viamrobotics/Rover-VR1/CAD/VR1-22-0026.SLDPRT

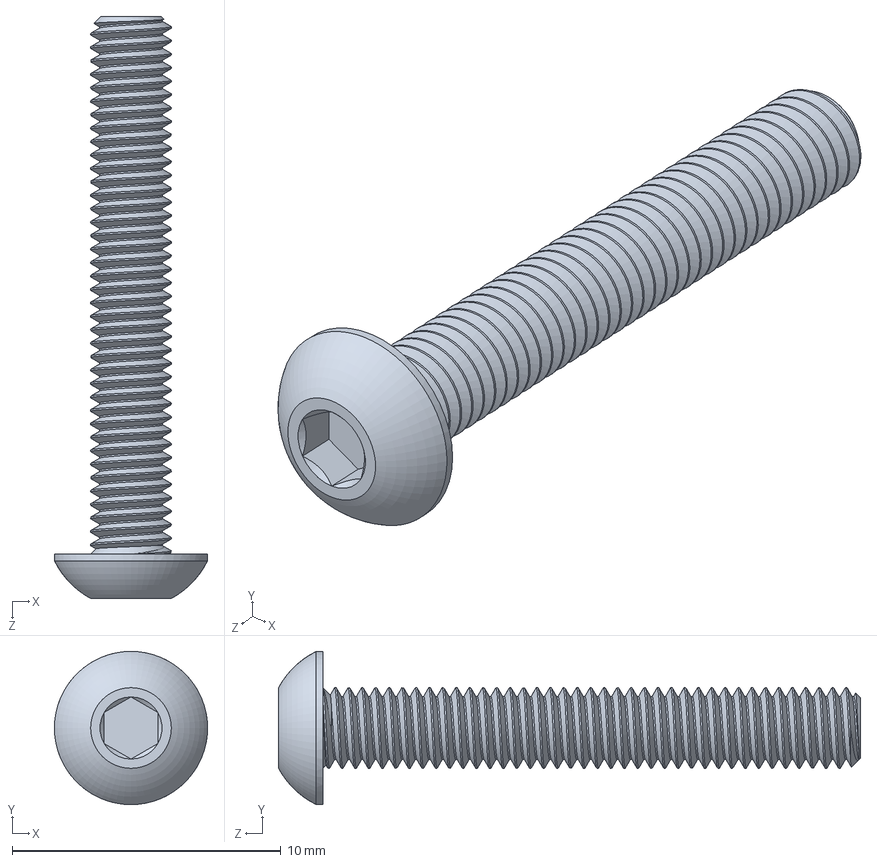
[picture p16: CAD file, 2023-01-20]
CAD/VR1-22-0026.SLDPRT
5.70 x 5.70 x 21.6 mm
