viamrobotics/Rover-VR1/CAD/VR1-22-0012.SLDPRT

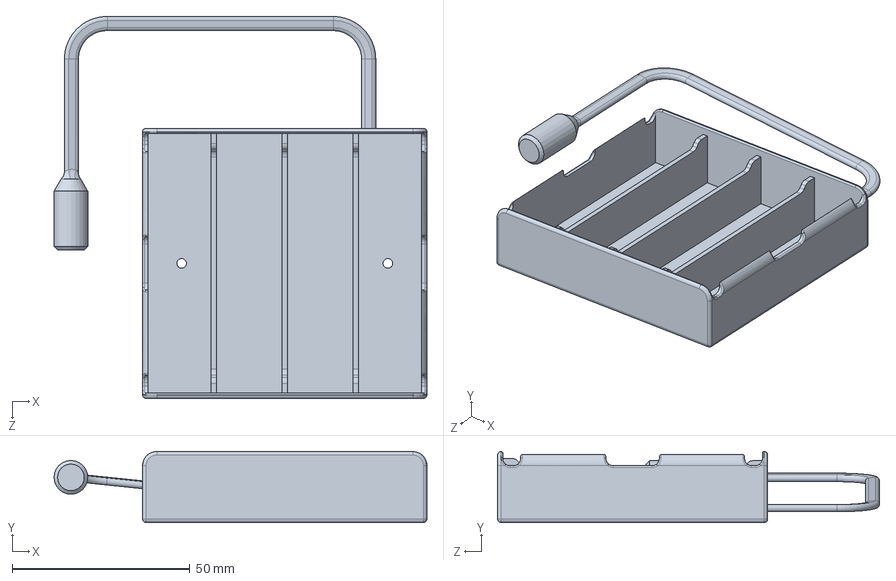
[picture p17: CAD file, 2023-01-20]
CAD/VR1-22-0012.SLDPRT
104.9 x 20.0 x 107.4 mm
