viamrobotics/Rover-VR1/CAD/VR1-22-0028.SLDPRT

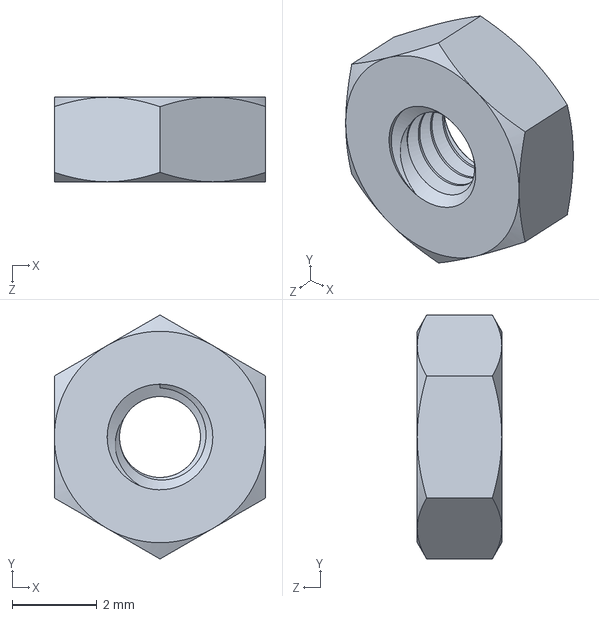
[picture p18: CAD file, 2023-01-20]
CAD/VR1-22-0028.SLDPRT
5.00 x 5.77 x 2.00 mm
