viamrobotics/Rover-VR1/CAD/VR1-22-0024.SLDPRT

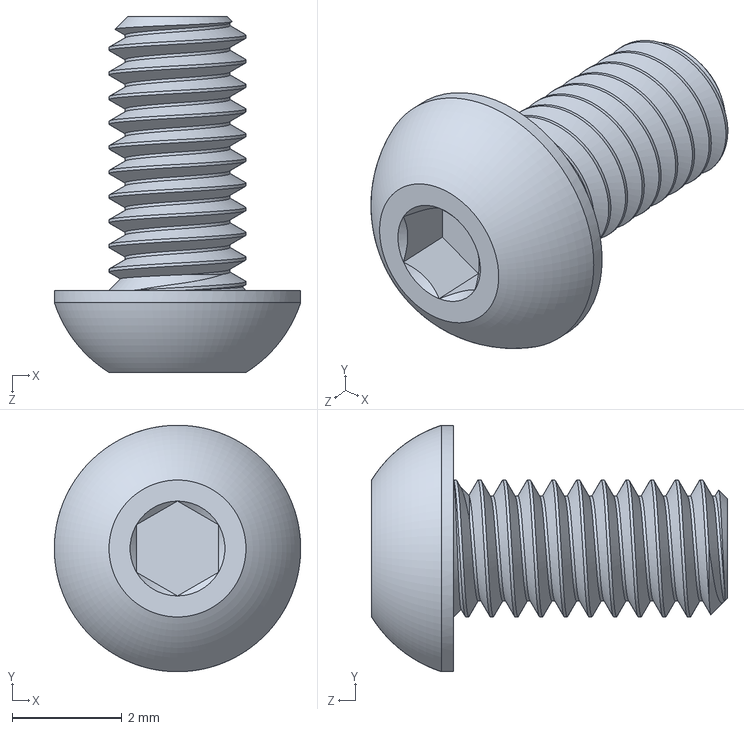
[picture p19: CAD file, 2023-01-20]
CAD/VR1-22-0024.SLDPRT
4.50 x 4.50 x 6.50 mm
