viamrobotics/Rover-VR1/CAD/VR1-22-0002.SLDPRT

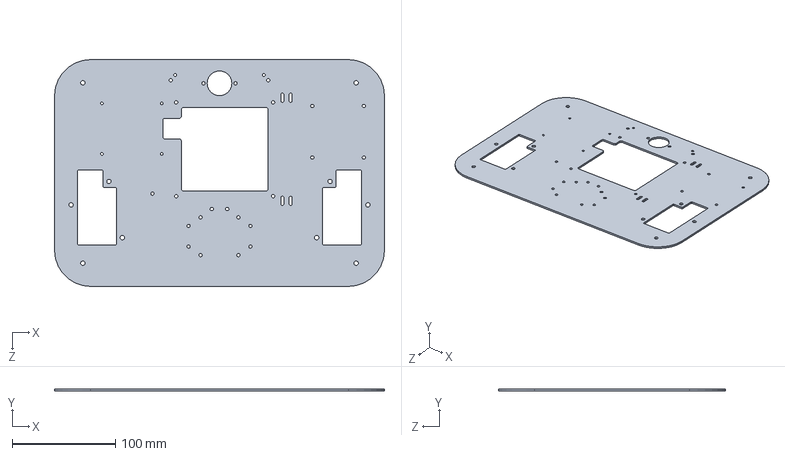
[picture p20: CAD file, 2023-01-20]
CAD/VR1-22-0002.SLDPRT
320.0 x 2.00 x 220.0 mm
