viamrobotics/Rover-VR1/CAD/VR1-22-0011-3dprintversion.SLDPRT

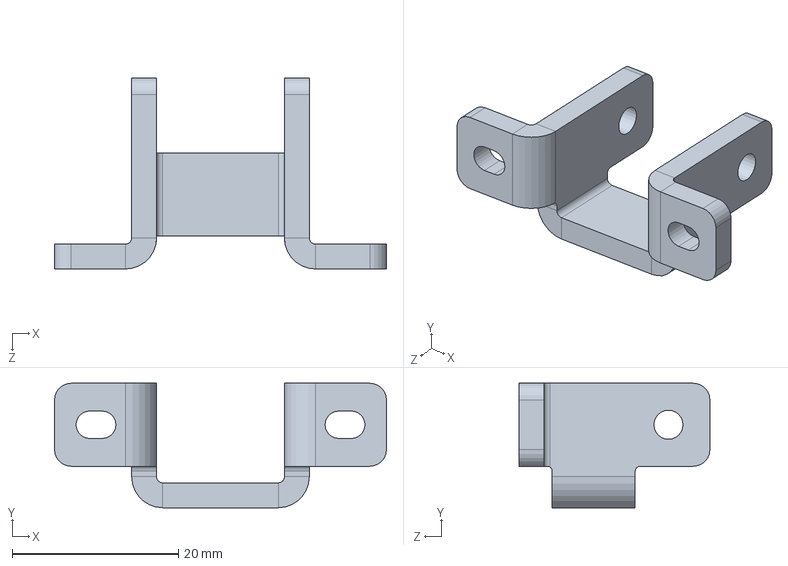
[picture p21: CAD file, 2023-01-20]
CAD/VR1-22-0011-3dprintversion.SLDPRT
40.0 x 15.0 x 23.0 mm
