viamrobotics/Rover-VR1/CAD/VR1-22-0021.SLDPRT

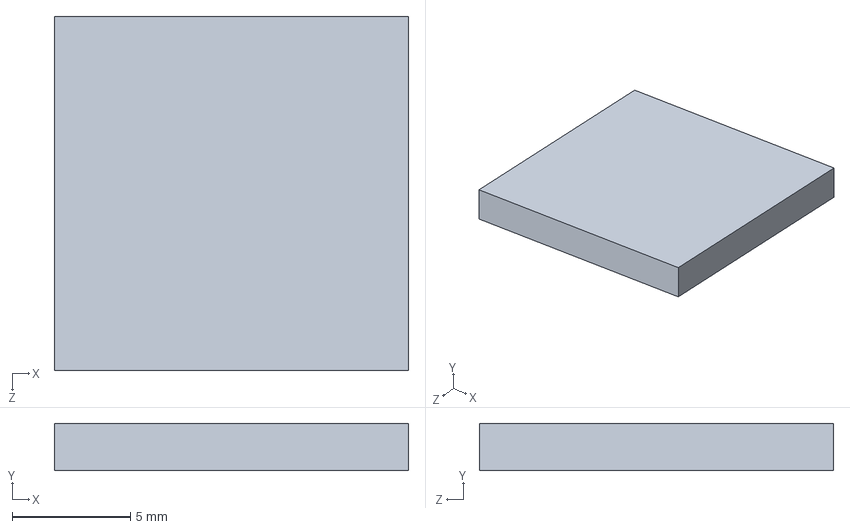
[picture p22: CAD file, 2023-01-20]
CAD/VR1-22-0021.SLDPRT
15.0 x 2.00 x 15.0 mm
