viamrobotics/Rover-VR1/CAD/VR1-22-0033.SLDPRT

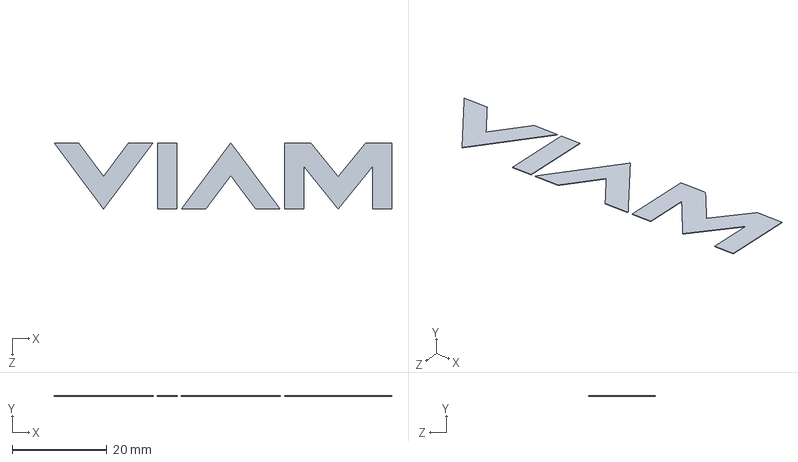
[picture p23: CAD file, 2023-01-20]
CAD/VR1-22-0033.SLDPRT
71.4 x 0.1 x 14.0 mm
