viamrobotics/Rover-VR1/CAD/VR1-22-0018.SLDPRT

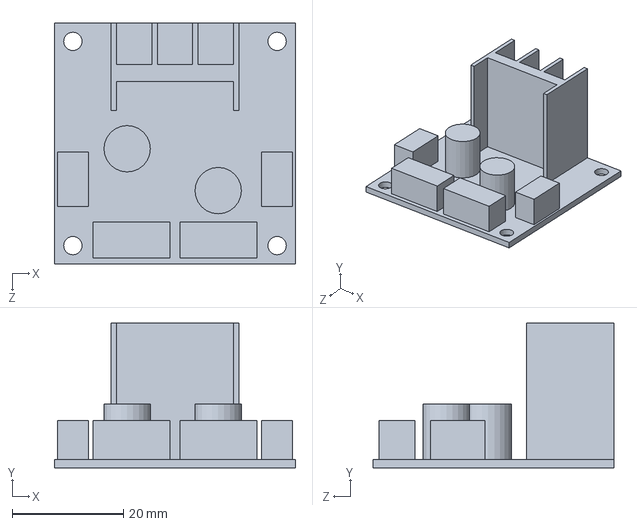
[picture p24: CAD file, 2023-01-20]
CAD/VR1-22-0018.SLDPRT
43.3 x 26.0 x 43.3 mm
