viamrobotics/Rover-VR1/CAD/VR1-22-0015.SLDPRT

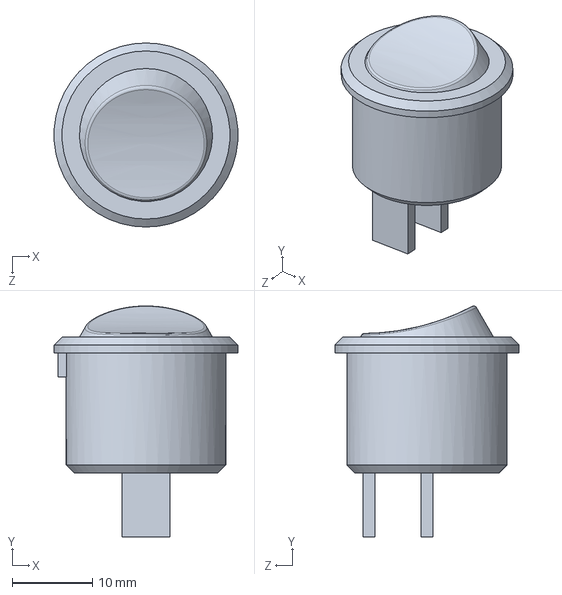
[picture p25: CAD file, 2023-01-20]
CAD/VR1-22-0015.SLDPRT
22.9 x 28.9 x 23.0 mm
