viamrobotics/Rover-VR1/CAD/VR1-22-0009.SLDPRT

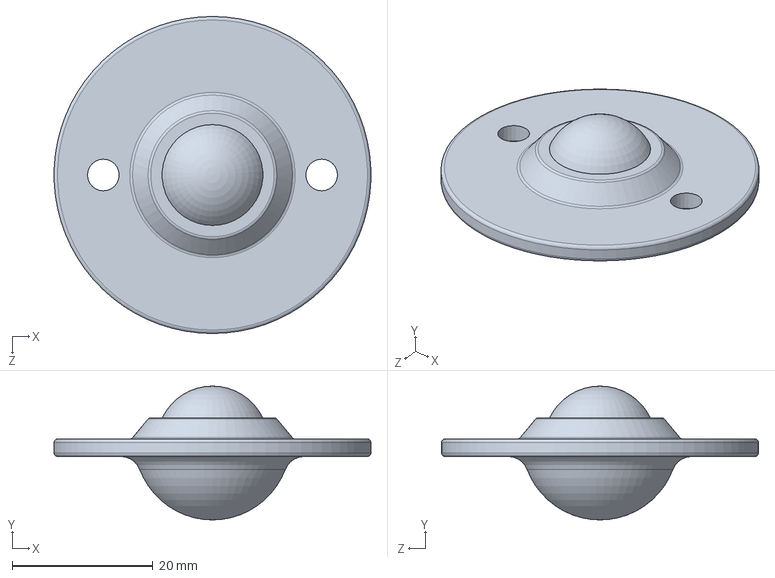
[picture p26: CAD file, 2023-01-20]
CAD/VR1-22-0009.SLDPRT
45.0 x 19.0 x 45.0 mm
