viamrobotics/Rover-VR1/CAD/VR1-22-0013.SLDPRT

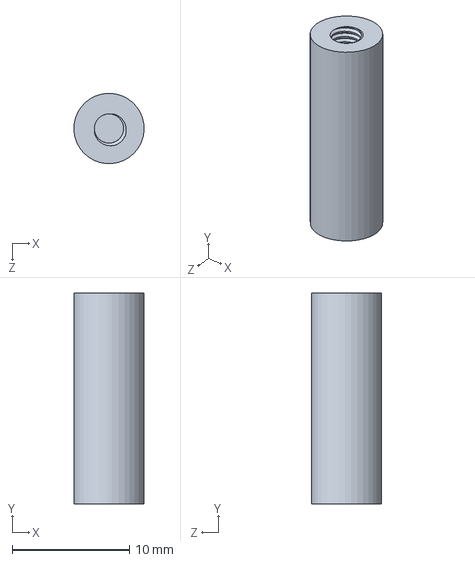
[picture p27: CAD file, 2023-01-20]
CAD/VR1-22-0013.SLDPRT
5.99 x 18.0 x 6.00 mm
