viamrobotics/Rover-VR1/CAD/VR1-22-0011_unfold.SLDPRT

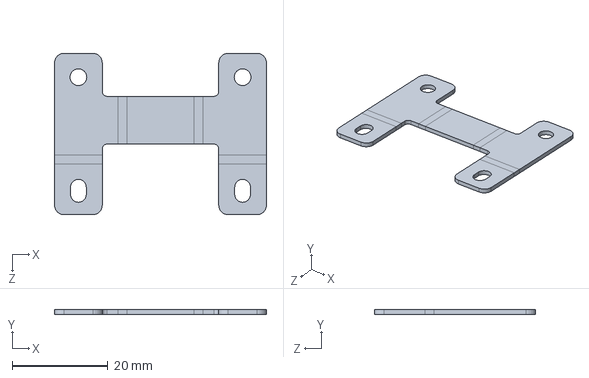
[picture p28: CAD file, 2023-01-20]
CAD/VR1-22-0011_unfold.SLDPRT
44.3 x 1 x 33.8 mm
