viamrobotics/Rover-VR1/CAD/VR1-22-0017.SLDPRT

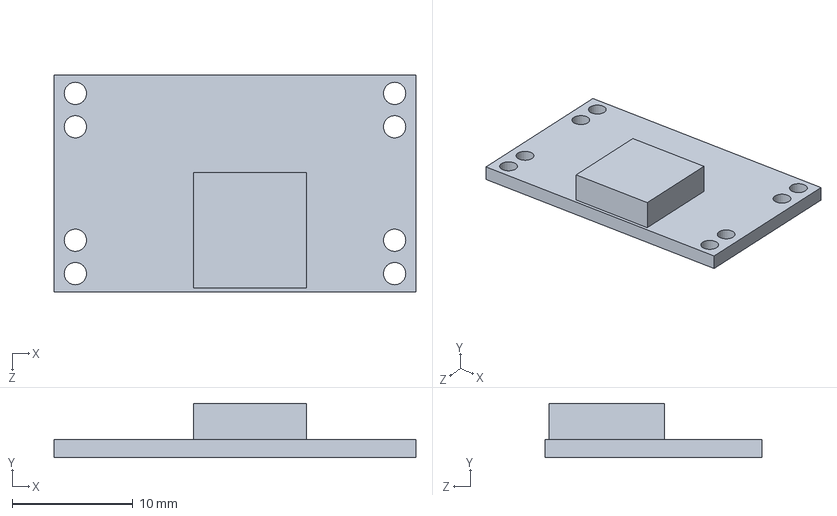
[picture p29: CAD file, 2023-01-20]
CAD/VR1-22-0017.SLDPRT
30.0 x 4.50 x 18.0 mm
