viamrobotics/Rover-VR1/CAD/VR1-22-0031e.SLDPRT

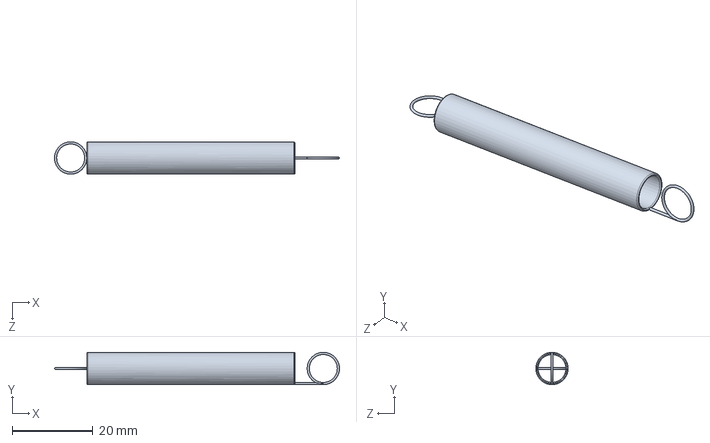
[picture p30: CAD file, 2023-01-20]
CAD/VR1-22-0031e.SLDPRT
70.5 x 8.00 x 8.00 mm
